brokenpotatoes/pico_strain/hal.c

/**
 * \copyright Copyright (C) 2019 Texas Instruments Incorporated - http://www.ti.com/
 *
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
 *    Redistributions of source code must retain the above copyright
 *    notice, this list of conditions and the following disclaimer.
 *
 *    Redistributions in binary form must reproduce the above copyright
 *    notice, this list of conditions and the following disclaimer in the
 *    documentation and/or other materials provided with the
 *    distribution.
 *
 *    Neither the name of Texas Instruments Incorporated nor the names of
 *    its contributors may be used to endorse or promote products derived
 *    from this software without specific prior written permission.
 *
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
 */

#include "hal.h"


//****************************************************************************
//
// Internal variables
//
//****************************************************************************

// Flag to indicate if a /DRDY interrupt has occurred
volatile bool flag_nDRDY_INTERRUPT = false;



//****************************************************************************
//
// Internal function prototypes
//
//****************************************************************************
void GPIO_DRDY_IRQHandler(uint gpio, uint32_t events);



//****************************************************************************
//
// External Functions (prototypes declared in hal.h)
//
//****************************************************************************


//****************************************************************************
//
// Timing functions
//
//****************************************************************************



//*****************************************************************************
//
//! Provides a timing delay with 'ms' resolution.
//!
//! \fn void delay_ms(const uint32_t delay_time_ms)
//!
//! \param delay_time_ms is the number of milliseconds to delay.
//!
//! \return None.
//
//*****************************************************************************
void delay_ms(const uint32_t delay_time_ms)
{
    /* --- INSERT YOUR CODE HERE --- */
    sleep_ms(delay_time_ms);
}



//*****************************************************************************
//
//! Provides a timing delay with 'us' resolution.
//!
//! \fn void delay_us(const uint32_t delay_time_us)
//!
//! \param delay_time_us is the number of microseconds to delay.
//!
//! \return None.
//
//*****************************************************************************
void delay_us(const uint32_t delay_time_us)
{
    /* --- INSERT YOUR CODE HERE --- */
    sleep_us(delay_time_us);
}




//****************************************************************************
//
// GPIO initialization
//
//****************************************************************************



//*****************************************************************************
//
//! Configures the MCU's GPIO pins that interface with the ADC.
//!
//! \fn void initGPIO(void)
//!
//! \return None.
//
//*****************************************************************************
void initGPIO(void)
{
    /* --- INSERT YOUR CODE HERE --- */
    // NOTE: Not all hardware implementations may control each of these pins...
    /* Configure the GPIO for 'CLK' as output and set clock output to something close to 8.192mhz*/
    clock_gpio_init(CLK_PIN, CLOCKS_CLK_GPOUT0_CTRL_AUXSRC_VALUE_CLK_SYS, 16);
    gpio_init(13);
    gpio_set_dir(13, GPIO_IN);
    /* Configure the GPIO for 'nSYNC_nRESET' as output and set high */
    gpio_init(nSYNC_nRESET_PIN);
    gpio_set_dir(nSYNC_nRESET_PIN, GPIO_OUT);
    gpio_put(nSYNC_nRESET_PIN, HIGH);   // Set high

    /* Configure the GPIO for 'nCS' as output and set high */
    gpio_init(nCS_PIN);
    gpio_set_dir(nCS_PIN, GPIO_OUT);
    gpio_put(nCS_PIN, HIGH);   // Set high

    /* Configure the GPIO for 'nDRDY' as input with falling edge interrupt */
    gpio_init(nDRDY_PIN);
    gpio_set_dir(nDRDY_PIN, GPIO_IN);
    gpio_set_irq_enabled_with_callback(nDRDY_PIN, GPIO_IRQ_EDGE_FALL, true, &GPIO_DRDY_IRQHandler);
}




//*****************************************************************************
//
// Interrupt handler for nDRDY GPIO
//
//*****************************************************************************



//*****************************************************************************
//
//! Interrupt handler for /DRDY falling edge interrupt.
//!
//! \fn void GPIO_DRDY_IRQHandler(void)
//!
//! \return None.
//
//*****************************************************************************
void GPIO_DRDY_IRQHandler(uint gpio, uint32_t events)
{
    /* --- INSERT YOUR CODE HERE --- */
    //NOTE: You many need to rename or register this interrupt function for your processor

    // Possible ways to handle this interrupt:
    // If you decide to read data here, you may want to disable other interrupts to avoid partial data reads.

    // In this example we set a flag and exit the interrupt routine. In the main program loop, your application can examine
    // all state flags and decide which state (operation) to perform next.

    flag_nDRDY_INTERRUPT = true;

    /* Clear interrupt */

    // NOTE: We add a short delay at the end to prevent re-entrance. Refer to E2E issue:
    // https://e2e.ti.com/support/microcontrollers/tiva_arm/f/908/p/332605/1786938#1786938
    //SysCtlDelay(3);
    //???
}




//****************************************************************************
//
// GPIO helper functions
//
//****************************************************************************



//*****************************************************************************
//
//! Reads that current state of the /CS GPIO pin.
//!
//! \fn bool getCS(void)
//!
//! \return boolean ('true' if /CS is high, 'false' if /CS is low).
//
//*****************************************************************************
bool getCS(void)
{
    /* --- INSERT YOUR CODE HERE --- */ 
    return (bool) gpio_get(nCS_PIN); 
}



//*****************************************************************************
//
//! Reads that current state of the nSYNC/nRESET GPIO pin.
//!
//! \fn bool getSYNC_RESET(void)
//!
//! \return boolean ('true' if nSYNC/nRESET is high, 'false' if nSYNC/nRESET is low).
//
//*****************************************************************************
bool getSYNC_RESET(void)
{
    /* --- INSERT YOUR CODE HERE --- */
    return (bool) gpio_get(nSYNC_nRESET_PIN);
}



//*****************************************************************************
//
//! Controls the state of the /CS GPIO pin.
//!
//! \fn void setCS(const bool state)
//!
//! \param state boolean indicating which state to set the /CS pin (0=low, 1=high)
//!
//! NOTE: The 'HIGH' and 'LOW' macros defined in hal.h can be passed to this
//! function for the 'state' parameter value.
//!
//! \return None.
//
//*****************************************************************************
void setCS(const bool state)
{
    /* --- INSERT YOUR CODE HERE --- */

    // td(CSSC) delay
    if(state) { sleep_us(2); }

    gpio_put(nCS_PIN, state);

    // td(SCCS) delay
    if(!state) { sleep_us(2); }
}



//*****************************************************************************
//
//! Controls the state of the nSYNC/nRESET GPIO pin.
//!
//! \fn void setSYNC_RESET(const bool state)
//!
//! \param state boolean indicating which state to set the nSYNC/nRESET pin (0=low, 1=high)
//!
//! NOTE: The 'HIGH' and 'LOW' macros defined in hal.h can be passed to this
//! function for the 'state' parameter value.
//!
//! \return None.
//
//*****************************************************************************
void setSYNC_RESET(const bool state)
{
    /* --- INSERT YOUR CODE HERE --- */
    gpio_put(nSYNC_nRESET_PIN, state);
}



//*****************************************************************************
//
//! Toggles the "nSYNC/nRESET" pin to trigger a synchronization
//! (LOW, delay 2 us, then HIGH).
//!
//! \fn void toggleSYNC(void)
//!
//! \return None.
//
//*****************************************************************************
void toggleSYNC(void)
{
    /* --- INSERT YOUR CODE HERE --- */
    gpio_put(nSYNC_nRESET_PIN, LOW);

    // nSYNC pulse width must be between 1 and 2,048 CLKIN periods
    delay_us(2);

    gpio_put(nSYNC_nRESET_PIN, HIGH);
}



//*****************************************************************************
//
//! Toggles the "nSYNC/nRESET" pin to trigger a reset
//! (LOW, delay 2 ms, then HIGH).
//!
//! \fn void toggleRESET(void)
//!
//! \return None.
//
//*****************************************************************************
void toggleRESET(void)
{
    /* --- INSERT YOUR CODE HERE --- */
    gpio_put(nSYNC_nRESET_PIN, LOW);

    // Minimum /RESET pulse width (tSRLRST) equals 2,048 CLKIN periods (1 ms @ 2.048 MHz)
    delay_ms(2);

    gpio_put(nSYNC_nRESET_PIN, HIGH);

    // tREGACQ delay before communicating with the device again
    delay_us(5);

    // NOTE: The ADS131M0x's next response word should be (0xFF20 | CHANCNT).
    // A different response may be an indication that the device did not reset.

    // Update register array
    restoreRegisterDefaults();

    // Write to MODE register to enforce mode settings
    writeSingleRegister(MODE_ADDRESS, MODE_DEFAULT);
}



//*****************************************************************************
//
//! Waits for the nDRDY interrupt or until the specified timeout occurs.
//!
//! \fn bool waitForDRDYinterrupt(const uint32_t timeout_ms)
//!
//! \param timeout_ms number of milliseconds to wait before timeout event.
//!
//! \return Returns 'true' if nDRDY interrupt occurred before the timeout.
//
//*****************************************************************************
bool waitForDRDYinterrupt(const uint32_t timeout_ms)
{
    /* --- INSERT YOUR CODE HERE ---
     * Poll the nDRDY GPIO pin until it goes low. To avoid potential infinite
     * loops, you may also want to implement a timer interrupt to occur after
     * the specified timeout period, in case the nDRDY pin is not active.
     * Return a boolean to indicate if nDRDY went low or if a timeout occurred.
     */

    // Convert ms to a # of loop iterations, OR even better use a timer here...
    uint32_t timeout = timeout_ms * 6000;   // convert to # of loop iterations

    // Reset interrupt flag
    flag_nDRDY_INTERRUPT = false;

    // Enable interrupts
    //IntMasterEnable();

    // Wait for nDRDY interrupt or timeout - each iteration is about 20 ticks
    do {
        timeout--;
    } while (!flag_nDRDY_INTERRUPT && (timeout > 0));

    // Reset interrupt flag
    flag_nDRDY_INTERRUPT = false;

    // Timeout counter greater than zero indicates that an interrupt occurred
    return (timeout > 0);
}




//****************************************************************************
//
// SPI Communication
//
//****************************************************************************



//*****************************************************************************
//
//! Configures the MCU's SPI peripheral, for interfacing with the ADC.
//!
//! \fn void initSPI(void)
//!
//! \return None.
//
//*****************************************************************************
void initSPI(void)
{
    /* --- INSERT YOUR CODE HERE ---
     * NOTE: The ADS131M0x operates in SPI mode 1 (CPOL = 0, CPHA = 1).
     */

    //
    // Enable clocks to GPIO Port Q and configure pins as SSI
    //
    spi_init(spi1, 25e6); // 25 MHz 
    spi_set_format(spi1, 8, 0, 1, SPI_MSB_FIRST);
    gpio_set_function(MISO_PIN, GPIO_FUNC_SPI);
    gpio_set_function(MOSI_PIN, GPIO_FUNC_SPI);
    gpio_set_function(SCK_PIN, GPIO_FUNC_SPI);
    

    //
    // Read any residual data from the SSI port.  This makes sure the receive
    // FIFOs are empty, so we don't read any unwanted junk.  This is done here
    // because the SPI SSI mode is full-duplex, which allows you to send and
    // receive at the same time.  The SSIDataGetNonBlocking function returns
    // "true" when data was returned, and "false" when no data was returned.
    // The "non-blocking" function checks if there is any data in the receive
    // FIFO and does not "hang" if there isn't.
    //
    //uint32_t junk;
    //while(MAP_SSIDataGetNonBlocking(SSI_BASE_ADDR, &junk));
}



//*****************************************************************************
//
//! Sends SPI byte array on MOSI pin and captures MISO data to a byte array.
//!
//! \fn void spiSendReceiveArrays(const uint8_t dataTx[], uint8_t dataRx[], const uint8_t byteLength)
//!
//! \param const uint8_t dataTx[] byte array of SPI data to send on MOSI.
//!
//! \param uint8_t dataRx[] byte array of SPI data captured on MISO.
//!
//! \param uint8_t byteLength number of bytes to send & receive.
//!
//! NOTE: Make sure 'dataTx[]' and 'dataRx[]' contain at least as many bytes of data,
//! as indicated by 'byteLength'.
//!
//! \return None.
//
//*****************************************************************************
void spiSendReceiveArrays(const uint8_t dataTx[], uint8_t dataRx[], const uint8_t byteLength)
{
    /*  --- INSERT YOUR CODE HERE ---
     *
     *  This function should send and receive multiple bytes over the SPI.
     *
     *  A typical SPI send/receive sequence may look like the following:
     *  1) Make sure SPI receive buffer is empty
     *  2) Set the /CS pin low (if controlled by GPIO)
     *  3) Send command bytes to SPI transmit buffer
     *  4) Wait for SPI receive interrupt
     *  5) Retrieve data from SPI receive buffer
     *  6) Set the /CS pin high (if controlled by GPIO)
     */

    // Require that dataTx and dataRx are not NULL pointers
    assert(dataTx && dataRx);

    // Set the nCS pin LOW
    setCS(LOW);

    // Send all dataTx[] bytes on MOSI, and capture all MISO bytes in dataRx[]
    int i;
    for (i = 0; i < byteLength; i++)
    {
        dataRx[i] = spiSendReceiveByte(dataTx[i]);
    }

    // Set the nCS pin HIGH
    setCS(HIGH);
}



//*****************************************************************************
//
//! Sends SPI byte on MOSI pin and captures MISO return byte value.
//!
//! \fn uint8_t spiSendReceiveByte(const uint8_t dataTx)
//!
//! \param const uint8_t dataTx data byte to send on MOSI pin.
//!
//! NOTE: This function is called by spiSendReceiveArrays(). If it is called
//! directly, then the /CS pin must also be directly controlled.
//!
//! \return Captured MISO response byte.
//
//*****************************************************************************
uint8_t spiSendReceiveByte(const uint8_t dataTx)
{
    /*  --- INSERT YOUR CODE HERE ---
     *  This function should send and receive single bytes over the SPI.
     *  NOTE: This function does not control the /CS pin to allow for
     *  more programming flexibility.
     */

    // Remove any residual or old data from the receive FIFO

    // SSI TX & RX
    uint8_t dataRx=0;
    spi_write_read_blocking(spi1, &dataTx, &dataRx, 1);
    return dataRx;
}
